anyo2002/tedun-digital-electronics-board/images/Power_sequence_F133A.png

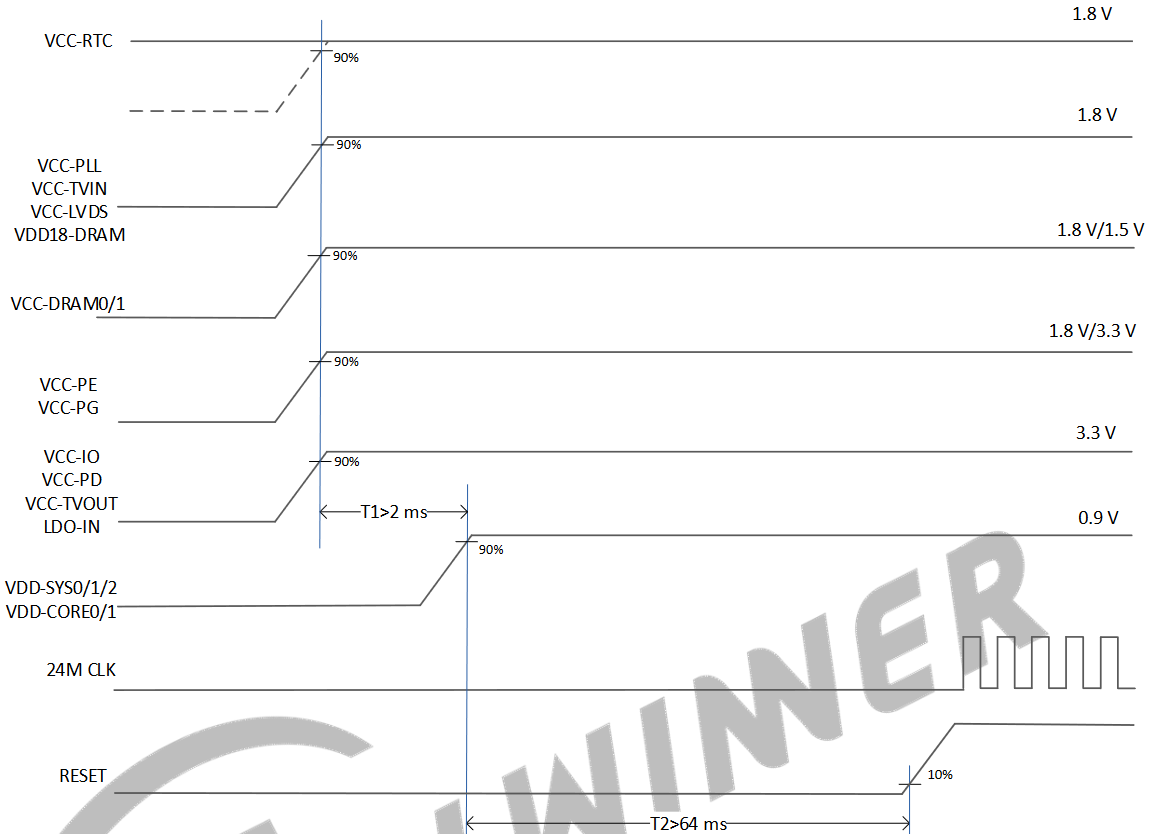
images/Power_sequence_F133A.png
